madworm/YauDL/gerber_files/PNGs/YauDL-B_SilkS.gbo.png

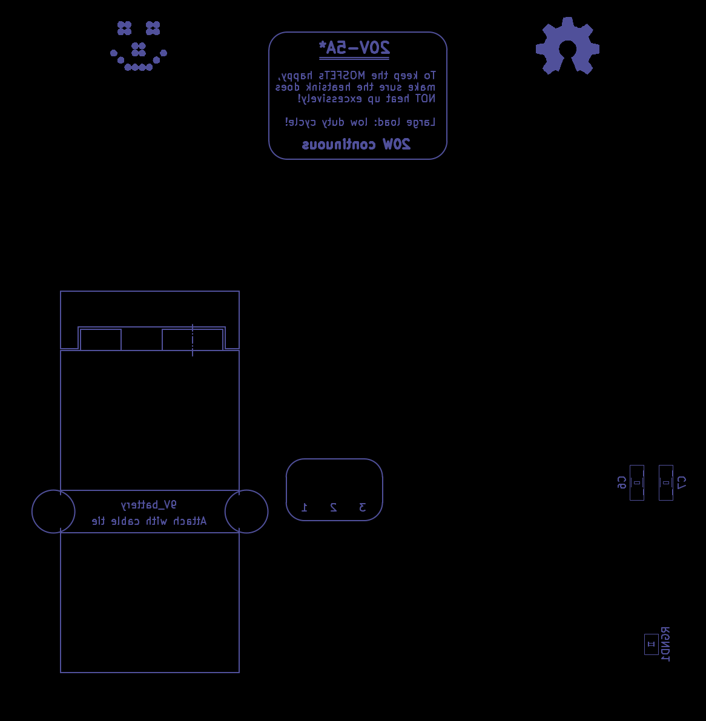
gerber_files/PNGs/YauDL-B_SilkS.gbo.png
