madworm/YauDL/gerber_files/PNGs/YauDL-Back.png

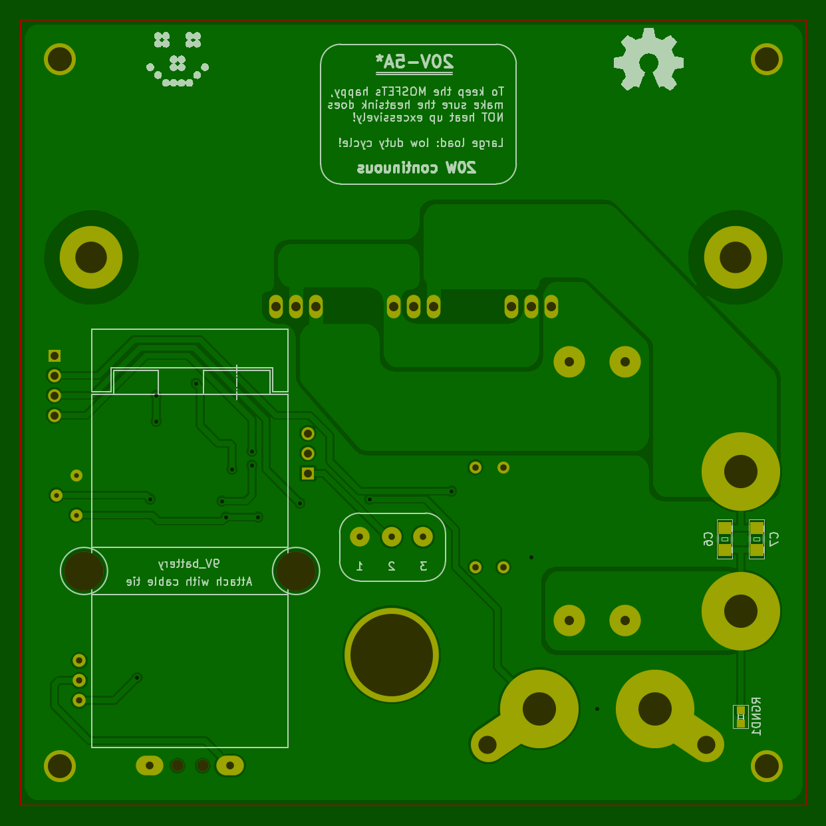
gerber_files/PNGs/YauDL-Back.png
