madworm/YauDL/gerber_files/PNGs/YauDL-F_SilkS.gto.png

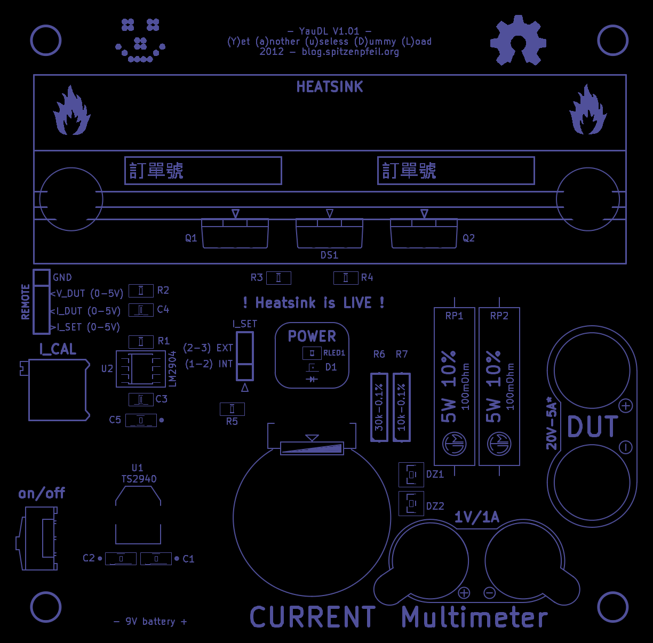
gerber_files/PNGs/YauDL-F_SilkS.gto.png
