madworm/YauDL/gerber_files/PNGs/YauDL.drl.png

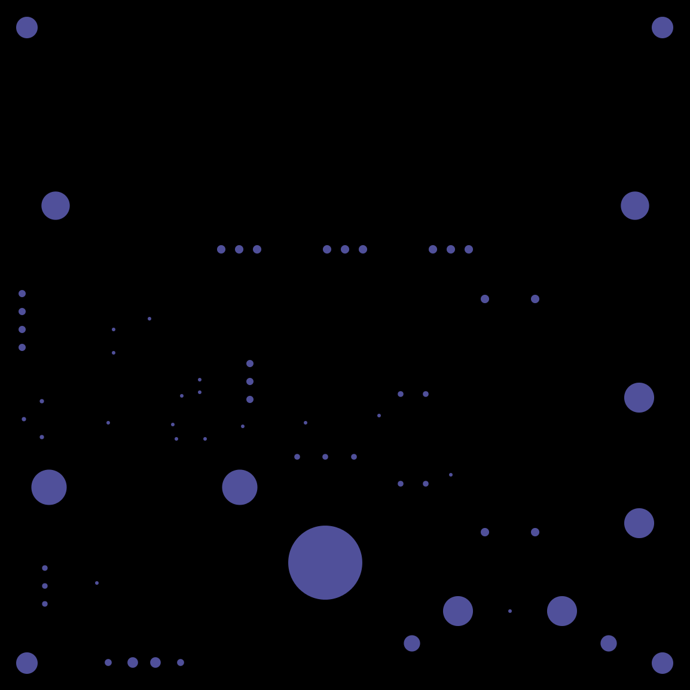
gerber_files/PNGs/YauDL.drl.png
